fmck3516/wirestat/schematics/wirestat.kicad_sch

## KiCad design schematics/wirestat.kicad_sch (2024-08-30)

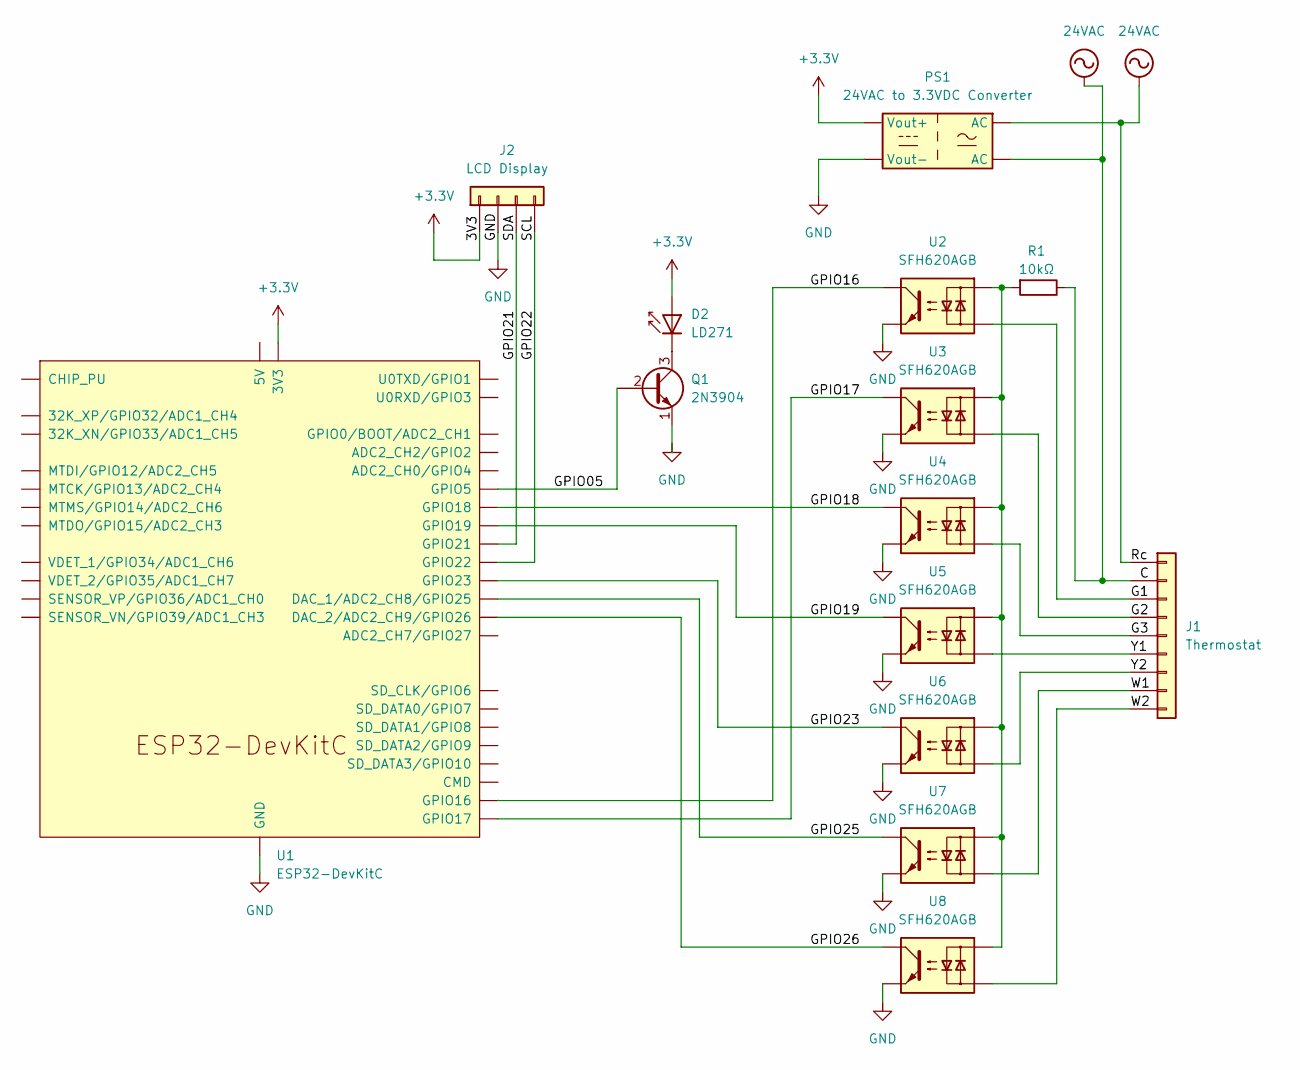
[picture p9: schematic wirestat.kicad_sch]

Parts:
D2: LD271; LED_D5.0mm_IRGrey
J1: Thermostat
J2: LCD Display
PS1: 24VAC to 3.3VDC Converter; Converter_ACDC_TRACO_TMLM-10-20_THT
Q1: 2N3904; TO-92_Inline
R1: 10kΩ
U1: ESP32-DevKitC
U2, U3, U4, U5, U6, U7, U8: SFH620AGB; SOP-4_4.4x2.6mm_P1.27mm

Connections:
24VAC: J1.1, J1.2, PS1.3 (AC), PS1.4 (AC), R1.1
+3.3V: D2.2 (A), J2.1, PS1.2 (Vout+), U1.1 (3V3)
G1: J1.3, U2.2
G2: J1.4, U3.2
G3: J1.5, U4.2
GND: J2.2, PS1.1 (Vout-), Q1.1 (E), U1.14 (GND), U1.32 (GND), U1.38 (GND), U2.3, U3.3, U4.3, U5.3, U6.3, U7.3, U8.3
GPIO05: Q1.2 (B), U1.29 (GPIO5)
GPIO16: U1.27 (GPIO16), U2.4
GPIO17: U1.28 (GPIO17), U3.4
GPIO18: U1.30 (GPIO18), U4.4
GPIO19: U1.31 (GPIO19), U5.4
GPIO21: J2.3, U1.33 (GPIO21)
GPIO22: J2.4, U1.36 (GPIO22)
GPIO23: U1.37 (GPIO23), U6.4
GPIO25: U1.9 (DAC_1/ADC2_CH8/GPIO25), U7.4
GPIO26: U1.10 (DAC_2/ADC2_CH9/GPIO26), U8.4
unnamed: D2.1 (K), Q1.3 (C)
unnamed: R1.2, U2.1, U3.1, U4.1, U5.1, U6.1, U7.1, U8.1
W1: J1.8, U7.2
W2: J1.9, U8.2
Y1: J1.6, U5.2
Y2: J1.7, U6.2
